finnhittson/PIC32Flex/hardware/PIC32Flex/PIC32Flex.kicad_sch

## KiCad design hardware/PIC32Flex/PIC32Flex.kicad_sch (2025-01-08)

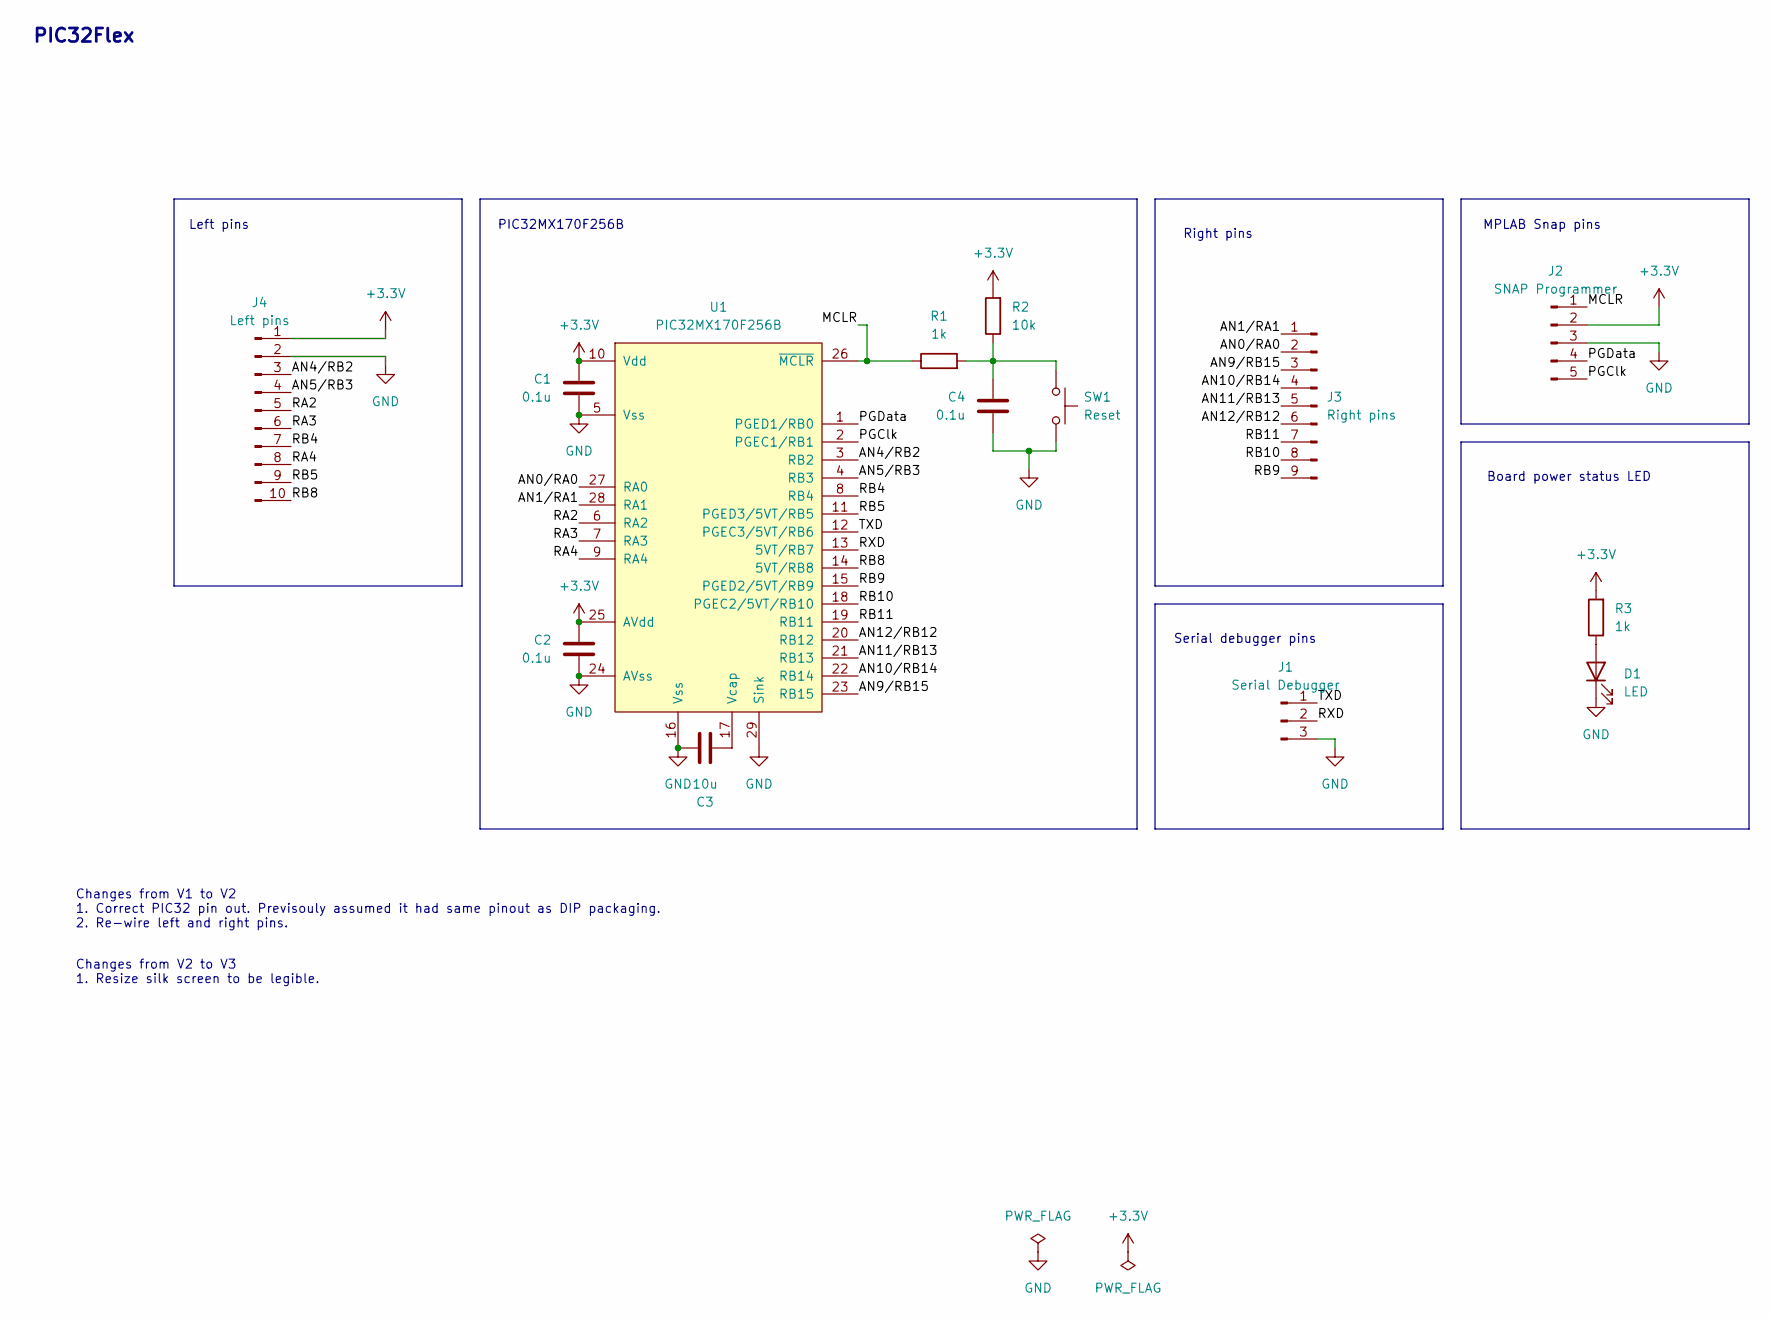
[picture p11: schematic PIC32Flex.kicad_sch]

Parts:
C1, C2, C4: 0.1u; C_0402_1005Metric
C3: 10u; C_0402_1005Metric
D1: LED; LED_0402_1005Metric
J1: Serial Debugger; PinSocket_1x03_P2.54mm_Vertical
J2: SNAP Programmer; PinSocket_1x05_P2.54mm_Vertical
J3: Right pins; PinSocket_1x09_P2.54mm_Vertical
J4: Left pins; PinSocket_1x10_P2.54mm_Vertical
R1, R3: 1k; R_0402_1005Metric
R2: 10k; R_0402_1005Metric
SW1: Reset; SW_PTS636_CNK
U1: PIC32MX170F256B; QFN28_6X6MC_MCH

Connections:
+3.3V: C1.2, C2.2, J2.2, J4.1, R2.2, R3.2, U1.10 (Vdd), U1.25 (AVdd)
AN0/RA0: J3.2, U1.27 (RA0)
AN1/RA1: J3.1, U1.28 (RA1)
AN4/RB2: J4.3, U1.3 (RB2)
AN5/RB3: J4.4, U1.4 (RB3)
AN9/RB15: J3.3, U1.23 (RB15)
AN10/RB14: J3.4, U1.22 (RB14)
AN11/RB13: J3.5, U1.21 (RB13)
AN12/RB12: J3.6, U1.20 (RB12)
GND: C1.1, C2.1, C3.2, C4.1, D1.1 (K), J1.3, J2.3, J4.2, SW1.2, U1.5 (Vss), U1.16 (Vss), U1.24 (AVss), U1.29 (Sink)
MCLR: J2.1, R1.1, U1.26 (~MCLR)
unnamed: C3.1, U1.17 (Vcap)
unnamed: C4.2, R1.2, R2.1, SW1.1
unnamed: D1.2 (A), R3.1
PGClk: J2.5, U1.2 (PGEC1/RB1)
PGData: J2.4, U1.1 (PGED1/RB0)
RA2: J4.5, U1.6 (RA2)
RA3: J4.6, U1.7 (RA3)
RA4: J4.8, U1.9 (RA4)
RB4: J4.7, U1.8 (RB4)
RB5: J4.9, U1.11 (PGED3/5VT/RB5)
RB8: J4.10, U1.14 (5VT/RB8)
RB9: J3.9, U1.15 (PGED2/5VT/RB9)
RB10: J3.8, U1.18 (PGEC2/5VT/RB10)
RB11: J3.7, U1.19 (RB11)
RXD: J1.2, U1.13 (5VT/RB7)
TXD: J1.1, U1.12 (PGEC3/5VT/RB6)

Notes on the sheet:
MPLAB Snap pins
Board power status LED
PIC32Flex
PIC32MX170F256B
Serial debugger pins
Right pins
Changes from V1 to V2 1. Correct PIC32 pin out. Previsouly assumed it had same pinout as DIP packaging. 2. Re-wire left and right pins.
Changes from V2 to V3 1. Resize silk screen to be legible.
Left pins
